anaobreja/TSC-Project/Images/Battery.png

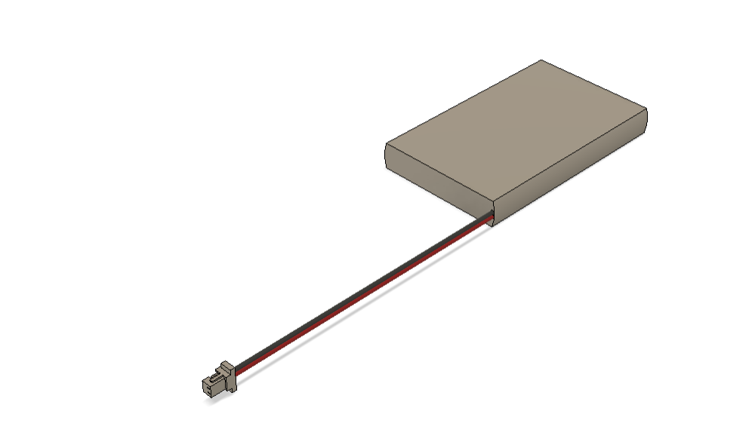
Images/Battery.png
