anaobreja/TSC-Project/Images/BLOCK Diagram.png

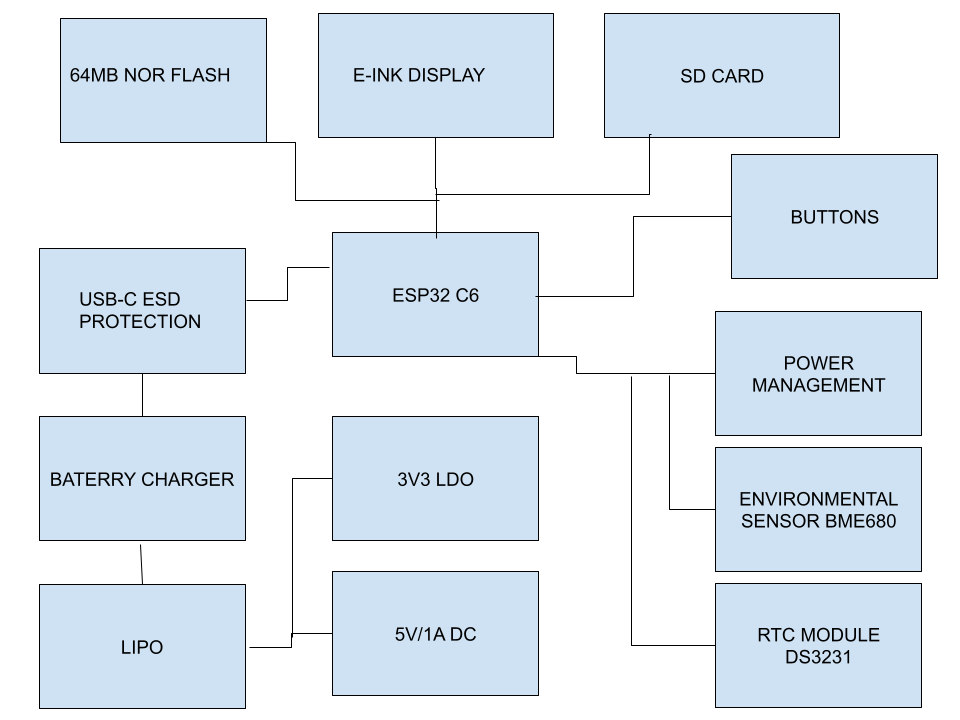
Images/BLOCK Diagram.png
