anaobreja/TSC-Project/Images/Display.png

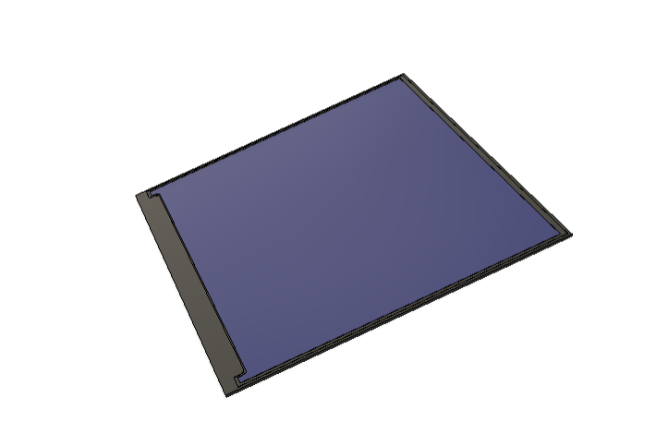
Images/Display.png
