anaobreja/TSC-Project/Images/Display_Opacity_80.png

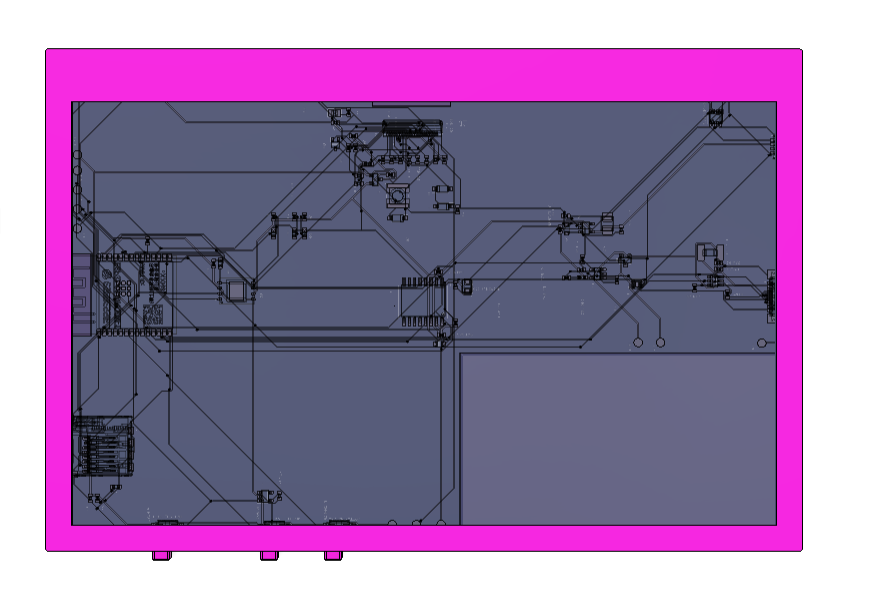
Images/Display_Opacity_80.png
