anaobreja/TSC-Project/Images/LID_HIDE.png

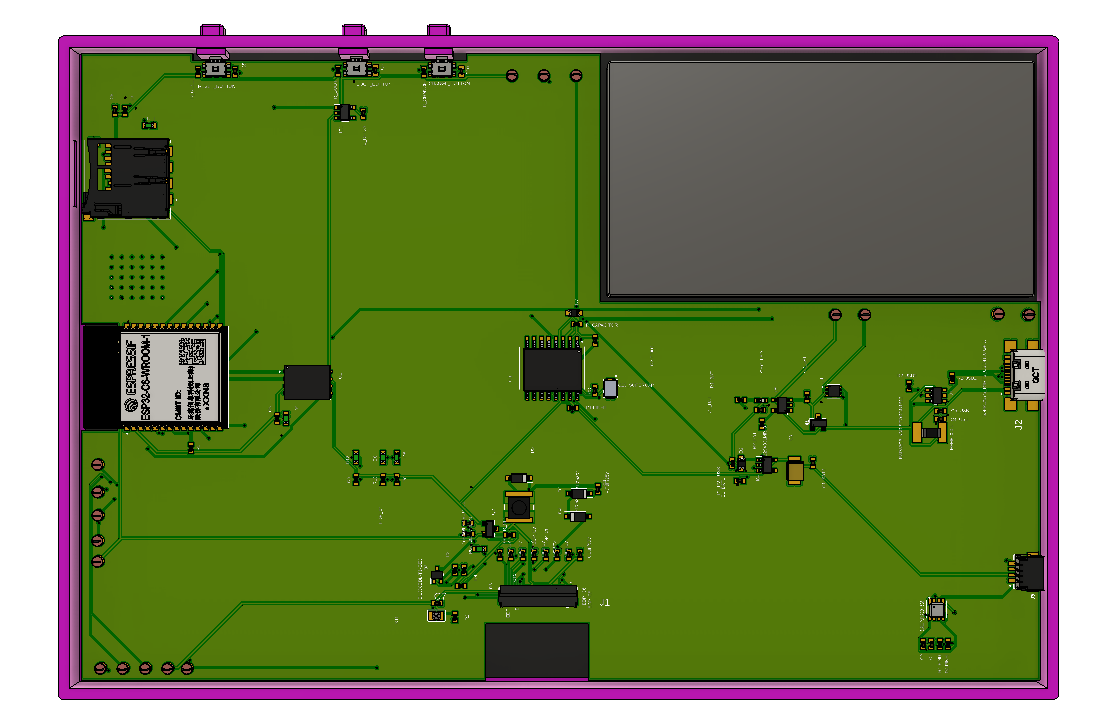
Images/LID_HIDE.png
