anaobreja/TSC-Project/Images/OpenBook2.png

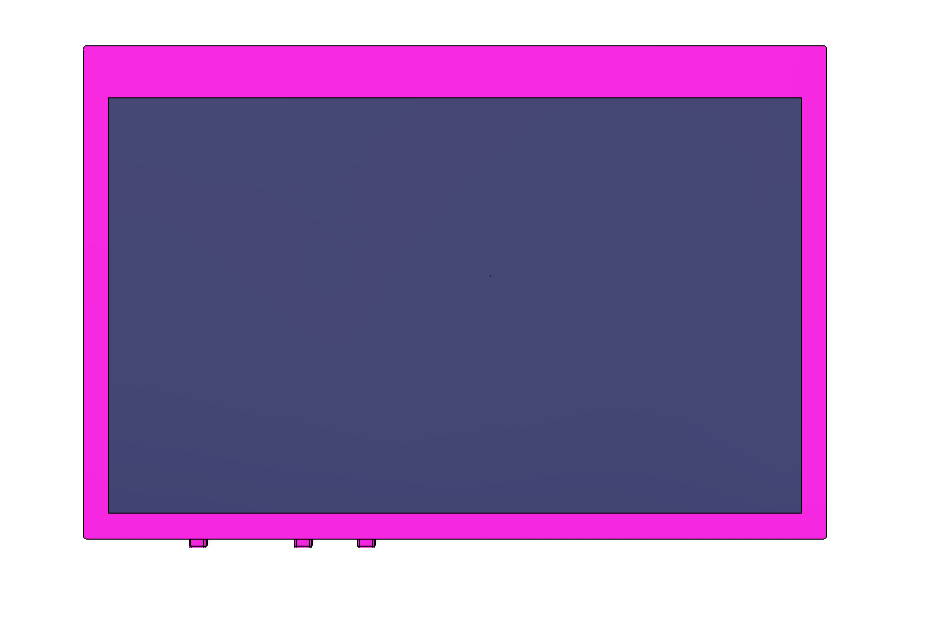
Images/OpenBook2.png
