anaobreja/TSC-Project/Images/OpenBook3.png

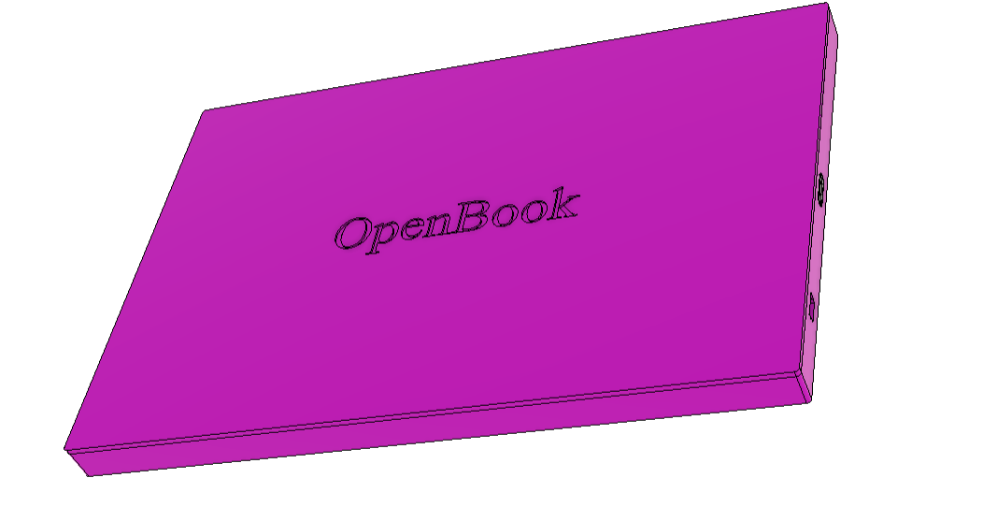
Images/OpenBook3.png
