anaobreja/TSC-Project/Images/OpenBook v6.png

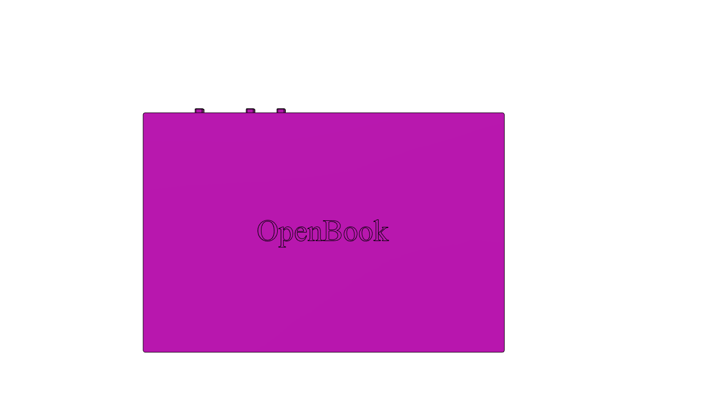
Images/OpenBook v6.png
