anaobreja/TSC-Project/Images/PCB.png

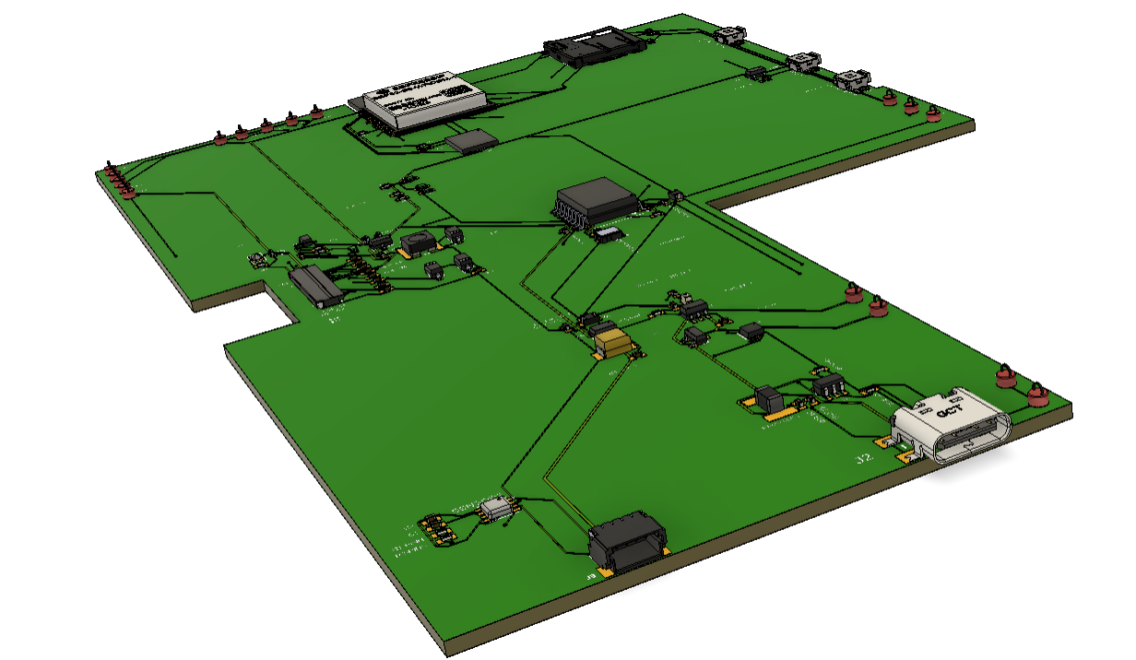
Images/PCB.png
