anaobreja/TSC-Project/Images/PCB_2D.png

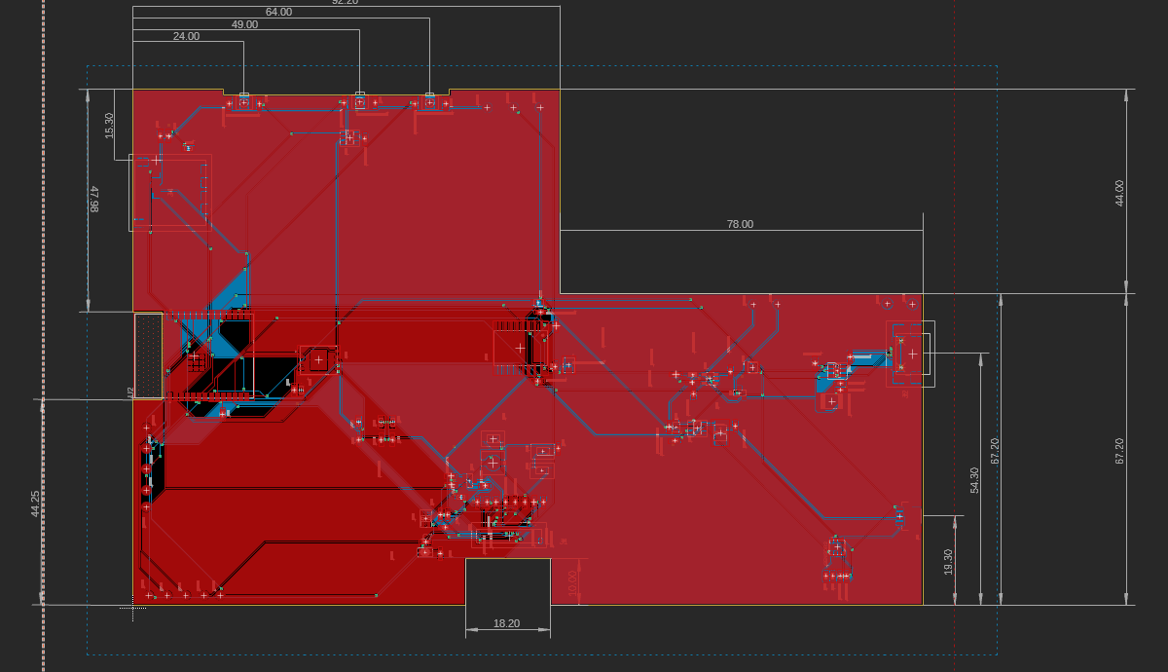
Images/PCB_2D.png
