anaobreja/TSC-Project/Images/PCB_BACK.png

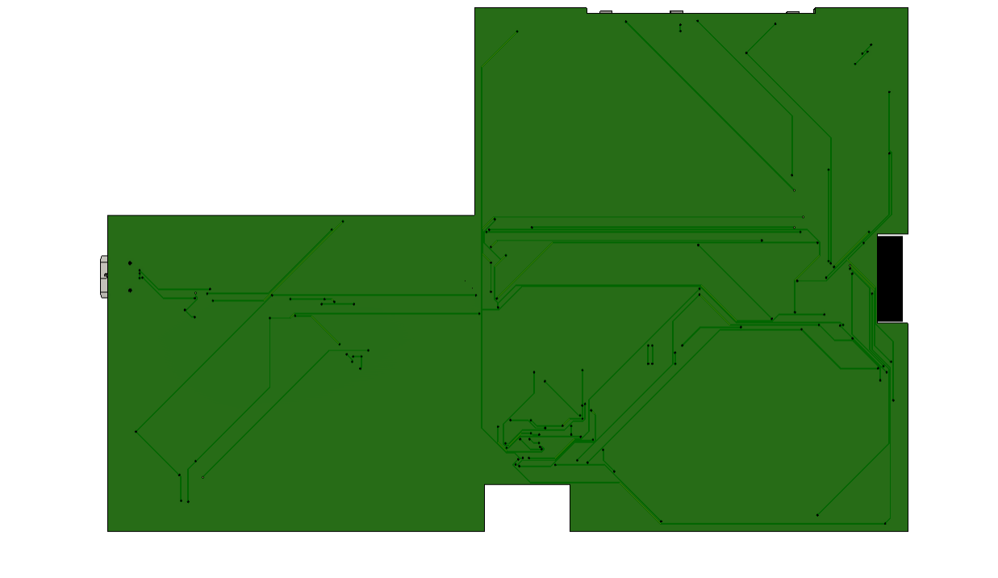
Images/PCB_BACK.png
