anaobreja/TSC-Project/Images/version2.png

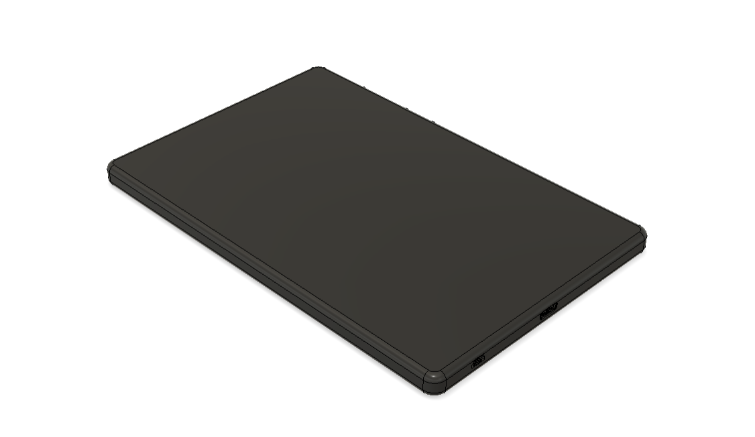
Images/version2.png
