anaobreja/TSC-Project/Images/version2_1.png

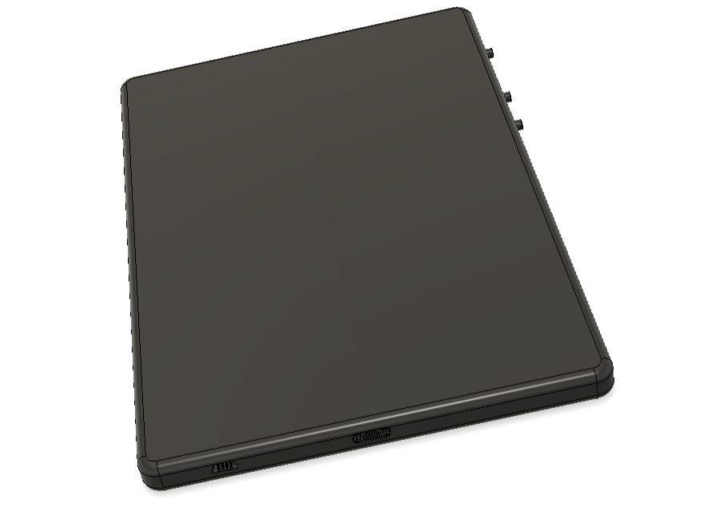
Images/version2_1.png
